atbrask/RealSIDShield/RealSIDShield/RealSIDShield.sch

## KiCad design RealSIDShield/RealSIDShield.sch (2013-12-30)

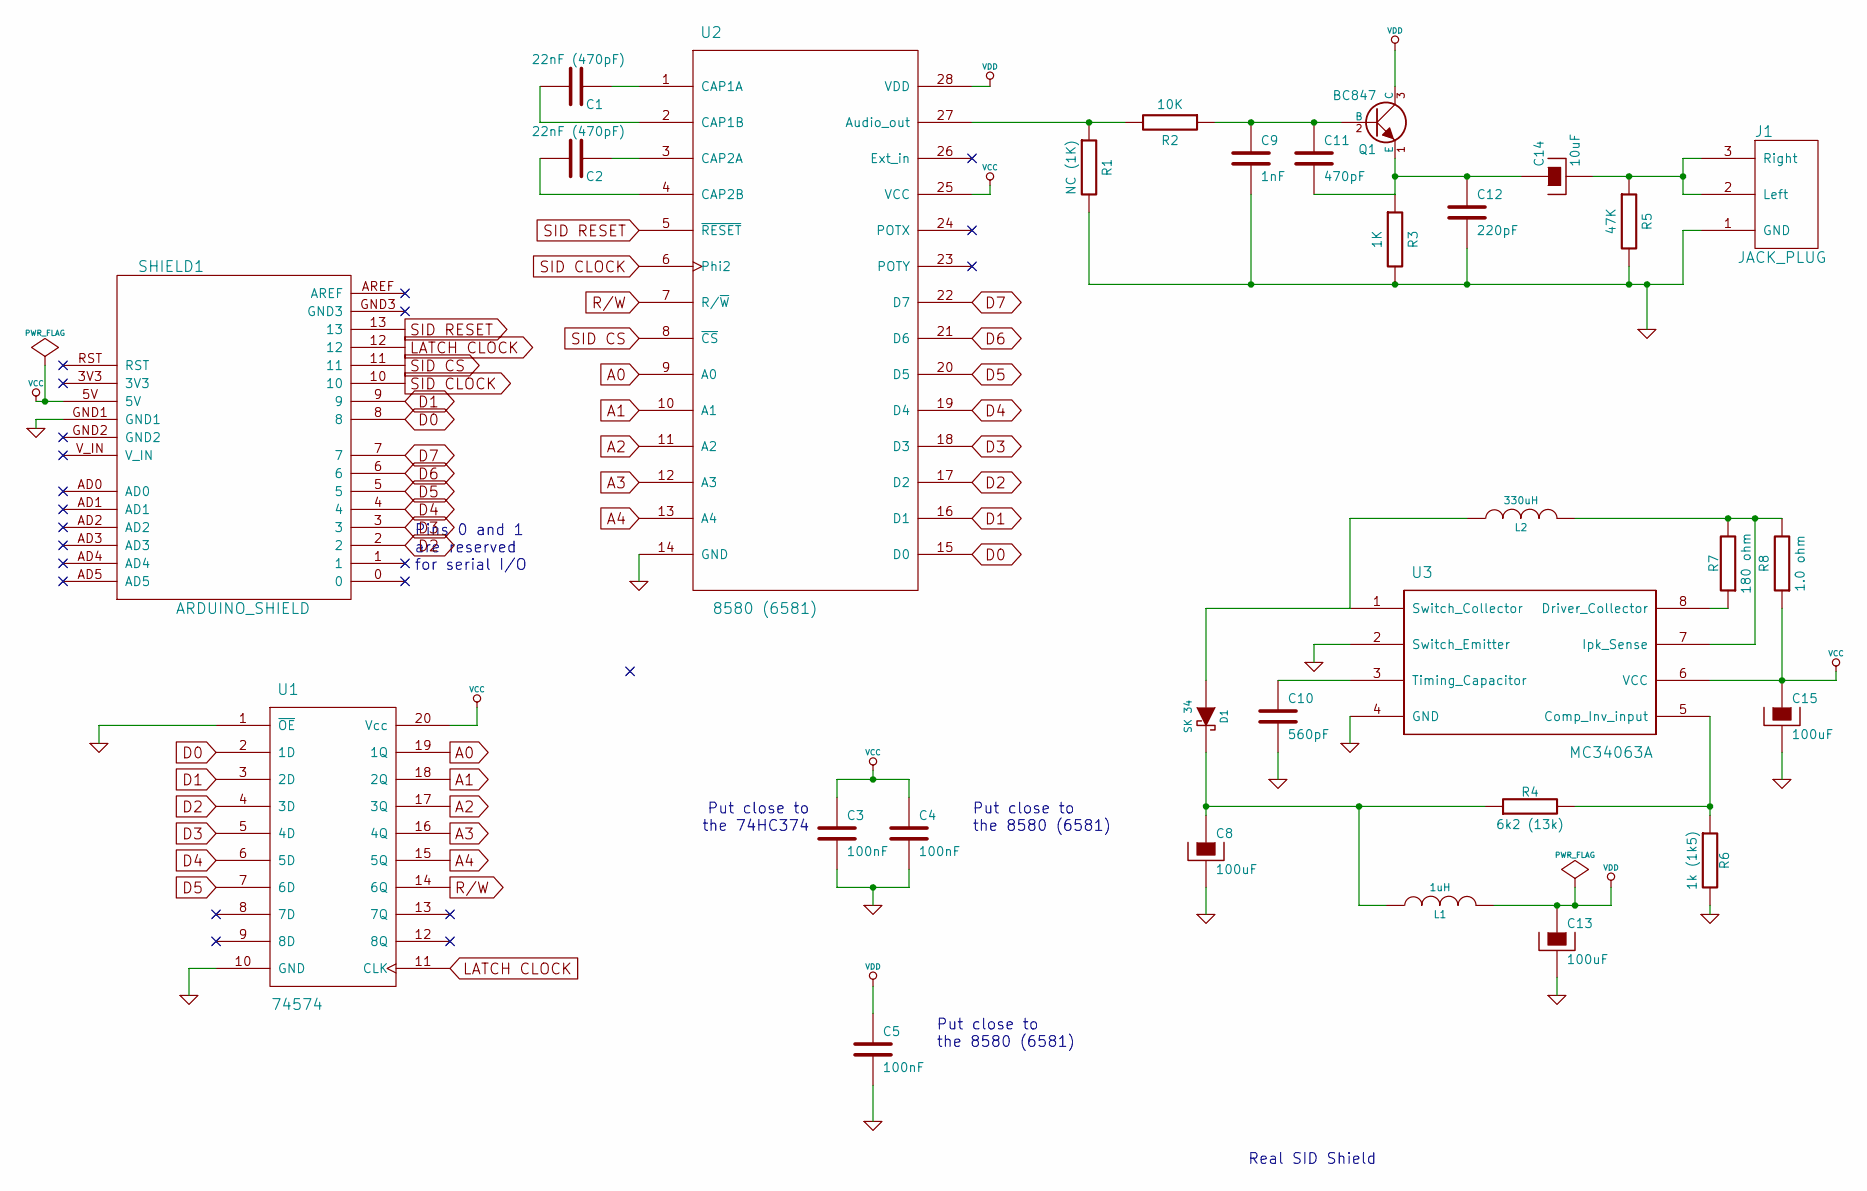
[picture p6: schematic RealSIDShield.sch]

Parts:
C1, C2: 22nF (470pF)
C3, C4, C5: 100nF
C8, C13, C15: 100uF
C9: 1nF
C10: 560pF
C11: 470pF
C12: 220pF
C14: 10uF
D1: SK 34
J1: JACK_PLUG
L1: 1uH
L2: 330uH
Q1: BC847
R1: NC (1K)
R2: 10K
R3: 1K
R4: 6k2 (13k)
R5: 47K
R6: 1k (1k5)
R7: 180 ohm
R8: 1.0 ohm
SHIELD1: ARDUINO_SHIELD
U1: 74574
U2: 8580 (6581)
U3: MC34063A

Connections:
A0: U1.19 (1Q), U2.9 (A0)
A1: U1.18 (2Q), U2.10 (A1)
A2: U1.17 (3Q), U2.11 (A2)
A3: U1.16 (4Q), U2.12 (A3)
A4: U1.15 (5Q), U2.13 (A4)
D0: SHIELD1.8, U1.2 (1D), U2.15 (D0)
D1: SHIELD1.9, U1.3 (2D), U2.16 (D1)
D2: SHIELD1.2, U1.4 (3D), U2.17 (D2)
D3: SHIELD1.3, U1.5 (4D), U2.18 (D3)
D4: SHIELD1.4, U1.6 (5D), U2.19 (D4)
D5: SHIELD1.5, U1.7 (6D), U2.20 (D5)
D6: SHIELD1.6, U2.21 (D6)
D7: SHIELD1.7, U2.22 (D7)
GND: C3.2, C4.2, C5.2, C8.2, C9.2, C10.2, C12.2, C13.2, C15.2, J1.1 (GND), R1.2, R3.2, R5.2, R6.2, SHIELD1.GND1, U1.1 (~OE), U1.10 (GND), U2.14 (GND), U3.2 (Switch_Emitter), U3.4 (GND)
LATCH CLOCK: SHIELD1.12, U1.11 (CLK)
unnamed: C1.1, U2.1 (CAP1A)
unnamed: C1.2, U2.2 (CAP1B)
unnamed: C2.1, U2.3 (CAP2A)
unnamed: C2.2, U2.4 (CAP2B)
unnamed: C8.1, D1.2 (K), L1.1, R4.1
unnamed: C10.1, U3.3 (Timing_Capacitor)
unnamed: C9.1, C11.1, Q1.2 (B), R2.1
unnamed: C11.2, C12.1, C14.1, Q1.1 (E), R3.1
unnamed: C14.2, J1.2 (Left), J1.3 (Right), R5.1
unnamed: D1.1 (A), L2.1, U3.1 (Switch_Collector)
unnamed: L2.2, R7.2, R8.2, U3.7 (Ipk_Sense)
unnamed: R1.1, R2.2, U2.27 (Audio_out)
unnamed: R4.2, R6.1, U3.5 (Comp_Inv_input)
unnamed: R7.1, U3.8 (Driver_Collector)
R/W: U1.14 (6Q), U2.7 (R/~W)
SID CLOCK: SHIELD1.10, U2.6 (Phi2)
SID CS: SHIELD1.11, U2.8 (~CS)
SID RESET: SHIELD1.13, U2.5 (~RESET)
VCC: C3.1, C4.1, C15.1, R8.1, SHIELD1.5V, U1.20 (Vcc), U2.25 (VCC), U3.6 (VCC)
VDD: C5.1, C13.1, L1.2, Q1.3 (C), U2.28 (VDD)

Notes on the sheet:
Put close to the 8580 (6581)
Put close to the 74HC374
Real SID Shield
Pins 0 and 1 are reserved for serial I/O
